shm-dmitry/climate_control_sensor/main/gpio/rgbled/rgbled.h

#ifndef MAIN_RGBLED_RGBLED_H_
#define MAIN_RGBLED_RGBLED_H_

#include "rgbled_def.h"

void rgbled_startup(const rgbled_config_t * config, const char * command_topic);

#endif /* MAIN_RGBLED_RGBLED_H_ */
