shm-dmitry/climate_control_sensor/main/log.h

#ifndef MAIN_LOG_H_
#define MAIN_LOG_H_

#include "esp_log.h"

#define TION_LOG "tion_log"
#define I2C_LOG "i2c_log"
#define WIFI_LOG "wifi_log"
#define MQTT_LOG "mqtt_log"
#define MH_Z19B_LOG "mh_z19b_log"
#define SNMP_LOG "snmp_log"
#define PMS7003_LOG "pms7003_log"
#define TOUCH_LOG "touch_log"
#define FAN_LOG "fan_log"
#define FAN_PWM_LOG "fan_pwm_log"
#define RGBLED_LOG "rgbled_log"
#define ANEMOMETER_LOG "anemometer_log"
#define VNS_LOG "nvs_log"
#define IR_LOG "ir_log"
#define BH1750_LOG "bh1750_log"
#define SGP30_LOG "sgp30_log"
#define BME280_LOG "bme280_log"

#endif /* MAIN_LOG_H_ */
