shm-dmitry/climate_control_sensor/main/gpio/fan_pwm/fan_pwm_nvs.h

#ifndef MAIN_GPIO_FAN_PWM_FAN_PWM_NVS_H_
#define MAIN_GPIO_FAN_PWM_FAN_PWM_NVS_H_

#include "stdint.h"

uint8_t fan_pwm_nws_read();

void fan_pwm_nws_write(uint8_t value);

#endif /* MAIN_GPIO_FAN_PWM_FAN_PWM_NVS_H_ */
