shm-dmitry/climate_control_sensor/main/gpio/rgbled/rgbled_def.h

#ifndef MAIN_RGBLED_RGBLED_DEF_H_
#define MAIN_RGBLED_RGBLED_DEF_H_

typedef struct rgbled_config_t {
	int gpio_red;
	int gpio_green;
	int gpio_blue;
} rgbled_config_t;

#endif /* MAIN_RGBLED_RGBLED_DEF_H_ */
